romansko/bsidestlv-2025-badge/src/include/armory.h

#ifndef __SECBOOT_H__
#define __SECBOOT_H__

void setupQuest();

int palisade();
int parapet();
int postern();
int persuasion();
void writeChallenge(char * challenge);
int attempts();
void plunderLoad();
int treasuryVisit();
void digForTreasure();

#endif // __SECBOOT_H__
