romansko/bsidestlv-2025-badge/src/include/cli.h

#ifndef __CLI_H__
#define __CLI_H__

#define CMD_SOLVE   "SOLVE"
#define CMD_ASSERT  "ASSERT"
#define CMD_RELEASE "RELEASE"
#define CMD_BEGIN   "BEGIN"
#define CMD_END     "END"
#define CMD_RESET   "RESET"
#define CMD_REBOOT  "REBOOT"
#define CMD_DATA    "DATA"

#endif // __CLI_H__
